Kikkiu17/espiot/software/STM32G030F6P6/ESPIOT/Core/ESP8266/esp8266.h

/*
 * esp8266.h
 *
 *  Created on: Apr 6, 2025
 *      Author: Kikkiu
 */

#ifndef ESP8266_ESP8266_H_
#define ESP8266_ESP8266_H_

#include "stm32g0xx_hal.h"
#include "usart.h"
#include "../settings.h"

extern bool WIFI_response_sent;

typedef enum
{
	GET 		= 'G',
	POST 		= 'P'
} Request_t;

typedef enum
{
	ERR 		= 0,
	TIMEOUT 	= 1,
	OK 			= 2,
	NULVAL		= 3,
	WAITING		= 4,
	FAIL		= 5,
} Response_t;

typedef struct
{
	char 		IP[15 + 1];
	char 		SSID[32 + 1];
	char		pw[64 + 1];
	char		buf[WIFI_BUF_MAX_SIZE + 1];
	char		hostname[HOSTNAME_MAX_SIZE + 1];
	char		name[NAME_MAX_SIZE + 1];
	char		time[8 + 1];	// hh:mm:ss
	int32_t	last_time_read;
} WIFI_t;

typedef struct
{
	WIFI_t* 	wifi;
	uint8_t 	connection_number;
 	Request_t	request_type;
	char		request[REQUEST_MAX_SIZE + 1];
	uint32_t	request_size;
	char		response_buffer[RESPONSE_MAX_SIZE + 1];
} Connection_t;

int32_t bufferToInt(char* buf, uint32_t size);

Response_t ESP8266_Init(void);
void ESP8266_ClearBuffer(void);
char* ESP8266_GetBuffer(void);
void ESP8266_HardwareReset(void);
Response_t ESP8266_ATReset(void);
Response_t ESP8266_CheckAT(void);
Response_t ESP8266_Restore(void);

Response_t ESP8266_WaitForStringCNDTROffset(char* str, int32_t offset, uint32_t timeout);
Response_t ESP8266_WaitForString(char* str, uint32_t timeout);
Response_t ESP8266_WaitKeepString(char* str, uint32_t timeout);

HAL_StatusTypeDef ESP8266_SendATCommandNoResponse(char* cmd, size_t size, uint32_t timeout);
Response_t ESP8266_SendATCommandResponse(char* cmd, size_t size, uint32_t timeout);
Response_t ESP8266_SendATCommandKeepString(char* cmd, size_t size, uint32_t timeout);
Response_t ESP8266_SendATCommandKeepStringNoResponse(char* cmd, size_t size);

/*
If the ESP is not connected to WiFi, this functions connects it to the WiFi specified by SSID and password
in the passed WIFI_t struct.
If it's already connected, it saves the current IP and SSID in the WIFI_t structure.
Note that this is a blocking function: if not connected to WiFi, it blocks until it connects or it timeouts (15 seconds)
*/
Response_t WIFI_Connect(WIFI_t* wifi);
Response_t WIFI_GetConnectionInfo(WIFI_t* wifi);
Response_t WIFI_SetCWMODE(uint8_t mode);
Response_t WIFI_SetCIPMUX(uint8_t mux);
Response_t WIFI_SetCIPSERVER(uint16_t server_port);
Response_t WIFI_SetHostname(WIFI_t* wifi, const char* hostname);
Response_t WIFI_GetHostname(WIFI_t* wifi);
Response_t WIFI_SetName(WIFI_t* wifi, char* name);
Response_t WIFI_GetIP(WIFI_t* wifi);
Response_t WIFI_SetIP(WIFI_t* wifi, char* ip);

Response_t WIFI_GetTime(WIFI_t* wifi);
int32_t WIFI_GetTimeHour(WIFI_t* wifi);
int32_t WIFI_GetTimeMinutes(WIFI_t* wifi);
int32_t WIFI_GetTimeSeconds(WIFI_t* wifi);

Response_t WIFI_ReceiveRequest(WIFI_t* wifi, Connection_t* conn, uint32_t timeout);
Response_t WIFI_SendResponse(Connection_t* conn, char* status_code, char* body, uint32_t body_length);
Response_t WIFI_EnableNTPServer(WIFI_t* wifi, int8_t time_offset);
void WIFI_ResetComm(WIFI_t* wifi, Connection_t* conn);
char* WIFI_RequestHasKey(Connection_t* conn, char* desired_key);
char* WIFI_RequestKeyHasValue(Connection_t* conn, char* request_key_ptr, char* value);
char* WIFI_GetKeyValue(Connection_t* conn, char* request_key_ptr, uint32_t* value_size);
Response_t WIFI_StartServer(WIFI_t* wifi, uint16_t port);
Response_t ESP8266_ResetWaitReady();
void WIFI_ResetConnectionIfError(WIFI_t* wifi, Connection_t* conn, Response_t wifistatus);

void WIFI_Init(WIFI_t* wifi);
void CONN_Init(Connection_t* conn);

#endif /* ESP8266_ESP8266_H_ */
